compukidmike/Saintcon2019/Firmware/Saintcon2019/Inc/keyboard.h

#include "stdint.h"
//Keyboard Pins
#define KBDA_Pin GPIO_PIN_2
#define KBDA_GPIO_Port GPIOE
#define KBDB_Pin GPIO_PIN_3
#define KBDB_GPIO_Port GPIOE
#define KBDC_Pin GPIO_PIN_4
#define KBDC_GPIO_Port GPIOE
#define KBDD_Pin GPIO_PIN_5
#define KBDD_GPIO_Port GPIOE
#define KBDE_Pin GPIO_PIN_6
#define KBDE_GPIO_Port GPIOE
#define KBDF_Pin GPIO_PIN_7
#define KBDF_GPIO_Port GPIOE
#define KBDG_Pin GPIO_PIN_8
#define KBDG_GPIO_Port GPIOE
#define KBDH_Pin GPIO_PIN_9
#define KBDH_GPIO_Port GPIOE
#define KBDI_Pin GPIO_PIN_10
#define KBDI_GPIO_Port GPIOE
#define KBDJ_Pin GPIO_PIN_11
#define KBDJ_GPIO_Port GPIOE
#define KBDK_Pin GPIO_PIN_12
#define KBDK_GPIO_Port GPIOE
#define KBDL_Pin GPIO_PIN_13
#define KBDL_GPIO_Port GPIOE
#define KBDM_Pin GPIO_PIN_14
#define KBDM_GPIO_Port GPIOE
#define KBDN_Pin GPIO_PIN_15
#define KBDN_GPIO_Port GPIOE
#define KBDO_Pin GPIO_PIN_0
#define KBDO_GPIO_Port GPIOD
#define KBDP_Pin GPIO_PIN_1
#define KBDP_GPIO_Port GPIOD
#define KBDQ_Pin GPIO_PIN_2
#define KBDQ_GPIO_Port GPIOD
#define KBDR_Pin GPIO_PIN_3
#define KBDR_GPIO_Port GPIOD
#define KBDS_Pin GPIO_PIN_4
#define KBDS_GPIO_Port GPIOD
#define KBDT_Pin GPIO_PIN_5
#define KBDT_GPIO_Port GPIOD
#define KBDU_Pin GPIO_PIN_6
#define KBDU_GPIO_Port GPIOD
#define KBDV_Pin GPIO_PIN_7
#define KBDV_GPIO_Port GPIOD
#define KBDW_Pin GPIO_PIN_9
#define KBDW_GPIO_Port GPIOD
#define KBDX_Pin GPIO_PIN_10
#define KBDX_GPIO_Port GPIOD
#define KBDY_Pin GPIO_PIN_11
#define KBDY_GPIO_Port GPIOD
#define KBDZ_Pin GPIO_PIN_12
#define KBDZ_GPIO_Port GPIOD

uint32_t keyboardUpdate();
uint32_t keyboardInstant();
