compukidmike/Saintcon2019/Firmware/Saintcon2019/Src/images.c

/*
 * images.c
 *
 *  Created on: Aug 25, 2019
 *      Author: compukidmike
 */

#include "stdint.h"
#include "images.h"

const uint8_t sc[] = {
		/*Pixel format: Fix 0xFF: 8 bit, Red: 8 bit, Green: 8 bit, Blue: 8 bit*/
		0x00, 0x00, 0x00, 0x00, 0x00, 0x00, 0x00, 0x00, 0x00, 0x00, 0x00, 0x00, 0x00, 0x00, 0x00, 0x00, 0x00, 0x00, 0x00, 0x00, 0x00, 0x00, 0x00, 0x00, 0x00, 0x00, 0x00, 0x00, 0x00, 0x00, 0x00, 0x00, 0x00, 0x00, 0x00, 0x00, 0xa6, 0xa6, 0xa6, 0xb8, 0xb8, 0xb8, 0xbc, 0xbc, 0xbc, 0xc1, 0xc1, 0xc1, 0xbf, 0xbf, 0xbf, 0xbc, 0xbc, 0xbc, 0xb1, 0xb1, 0xb1, 0xb1, 0xb1, 0xb1, 0xbc, 0xbc, 0xbc, 0xbf, 0xbf, 0xbf, 0xc1, 0xc1, 0xc1, 0xbf, 0xbf, 0xbf, 0xb8, 0xb8, 0xb8, 0xa4, 0xa4, 0xa4, 0x00, 0x00, 0x00, 0x00, 0x00, 0x00, 0x00, 0x00, 0x00, 0x00, 0x00, 0x00, 0x00, 0x00, 0x00, 0x00, 0x00, 0x00, 0x00, 0x00, 0x00, 0x00, 0x00, 0x00, 0x00, 0x00, 0x00, 0x00, 0x00, 0x00, 0x00, 0x00, 0x00, 0x00, 0x00, 0x00,
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
};
