compukidmike/Saintcon2019/Firmware/Saintcon2019/Inc/eeprom_emul_conf.h

/**
  ******************************************************************************
  * @file    eeprom_emul_conf.h
  * @author  MCD Application Team
  * @brief   EEPROM emulation configuration file.
  *          This file should be copied to the application folder and renamed
  *          to eeprom_emul_conf.h.
  ******************************************************************************
  * @attention
  *
  * <h2><center>&copy; Copyright (c) 2017 STMicroelectronics International N.V.
  * All rights reserved.</center></h2>
  *
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
  ******************************************************************************
  */

/** @addtogroup EEPROM_Emulation
  * @{
  */

/* Define to prevent recursive inclusion -------------------------------------*/
#ifndef __EEPROM_EMUL_CONF_H
#define __EEPROM_EMUL_CONF_H

#ifdef __cplusplus
 extern "C" {
#endif

/* Private constants ---------------------------------------------------------*/
/** @addtogroup EEPROM_Private_Constants
  * @{
  */

/** @defgroup Private_Configuration_Constants Private Configuration Constants
  * @{
  */

/* Configuration of eeprom emulation in flash, can be custom */
#define START_PAGE_ADDRESS      0x08028000U /*!< Start address of the 1st page in flash, for EEPROM emulation */
#define CYCLES_NUMBER           1U   /*!< Number of 10Kcycles requested, minimum 1 for 10Kcycles (default),
                                        for instance 10 to reach 100Kcycles. This factor will increase
                                        pages number */
#define GUARD_PAGES_NUMBER      0U   /*!< Number of guard pages avoiding frequent transfers (must be multiple of 2): 0,2,4.. */

/* Configuration of crc calculation for eeprom emulation in flash */
#define CRC_POLYNOMIAL_LENGTH   LL_CRC_POLYLENGTH_16B /* CRC polynomial lenght 16 bits */
#define CRC_POLYNOMIAL_VALUE    0x8005U /* Polynomial to use for CRC calculation */

/**
  * @}
  */

/**
  * @}
  */

/* Exported types ------------------------------------------------------------*/
/* Exported constants --------------------------------------------------------*/
/** @defgroup EEPROM_Exported_Constants EEPROM Exported Constants
  * @{
  */

/** @defgroup Exported_Configuration_Constants Exported Configuration Constants
  * @{
  */
#define NB_OF_VARIABLES         260U  /*!< Number of variables to handle in eeprom */

 //eeprom variable map
#define EEP_CHALLENGE_LEVEL 1 //1 byte
#define EEP_CUSTOM_MESSAGE_LENGTH 2 //Up to 255
#define EEP_CUSTOM_MESSAGE_START 3 //1-255
#define EEP_MINIBADGE_STATE 259 //1 byte
#define EEP_MESSAGE_CODE_1 258 //6 bytes
#define EEP_MESSAGE_CODE_2 264 //6 bytes
#define EEP_MESSAGE_CODE_3 270 //6 bytes
#define EEP_MESSAGE_CODE_4 276 //6 bytes
#define EEP_MESSAGE_CODE_5 282 //6 bytes
#define EEP_MESSAGE_CODE_6 288 //6 bytes
#define EEP_MESSAGE_CODE_7 294 //6 bytes
#define EEP_MESSAGE_CODE_8 300 //6 bytes
#define EEP_MESSAGE_CODE_9 306 //6 bytes
#define EEP_LEVEL_1_MESSAGE_LENGTH 336 //1 byte
#define EEP_LEVEL_1_MESSAGE_START 337 //Up to 255
#define EEP_LEVEL_2_MESSAGE_LENGTH 592 //1 byte
#define EEP_LEVEL_2_MESSAGE_START 593 //Up to 255
#define EEP_LEVEL_3_MESSAGE_LENGTH 848 //1 byte
#define EEP_LEVEL_3_MESSAGE_START 849 //Up to 255
#define EEP_FINAL_MESSAGE_LENGTH 1104 //1 byte
#define EEP_FINAL_MESSAGE_START 1105 //Up to 255



/**
  * @}
  */

/**
  * @}
  */

#ifdef __cplusplus
}
#endif

/**
  * @}
  */

#endif /* __EEPROM_EMUL_CONF_H */


/************************ (C) COPYRIGHT STMicroelectronics *****END OF FILE****/
