compukidmike/Saintcon2019/Firmware/Saintcon2019/Inc/snake_images.h

#ifndef SNAKE_IMAGES_H
#define SNAKE_IMAGES_H
static const uint8_t image_data_snake[126] = {
    // ∙▓▓∙∙∙
    // ▒▒▒▒∙∙
    // ∙∙▒▒∙∙
    // ∙∙▒▒∙∙
    // ∙▒▒∙∙▓
    // ▓▒░∙∙▓
    // ∙▒░░░∙
	//6x7
	    0x00, 0x00, 0x00, 0x35, 0xb0, 0x32, 0x00, 0x8e, 0x00, 0x00, 0x00, 0x00, 0x00, 0x00, 0x00, 0x00, 0x00, 0x00,
	    0x2a, 0xd1, 0x21, 0x2a, 0xd1, 0x21, 0x2a, 0xd1, 0x21, 0x2a, 0xd1, 0x21, 0x00, 0x00, 0x00, 0x00, 0x00, 0x00,
	    0x00, 0x00, 0x00, 0x00, 0x00, 0x00, 0x00, 0xfe, 0x00, 0x2a, 0xd1, 0x21, 0x00, 0x00, 0x00, 0x00, 0x00, 0x00,
	    0x00, 0x00, 0x00, 0x00, 0x00, 0x00, 0x00, 0xfe, 0x00, 0x2a, 0xd1, 0x21, 0x00, 0x00, 0x00, 0x00, 0x00, 0x00,
	    0x00, 0x00, 0x00, 0x00, 0xfe, 0x00, 0x00, 0xfe, 0x00, 0x00, 0x00, 0x00, 0x00, 0x00, 0x00, 0x2a, 0xd1, 0x21,
	    0x2a, 0xd1, 0x21, 0x00, 0xfe, 0x00, 0x00, 0x8e, 0x00, 0x00, 0x00, 0x00, 0x00, 0x00, 0x00, 0x2a, 0xd1, 0x21,
	    0x00, 0x00, 0x00, 0x2a, 0xd1, 0x21, 0x00, 0x8e, 0x00, 0x00, 0x8e, 0x00, 0x3c, 0x6a, 0x44, 0x00, 0x00, 0x00
};
#endif
